Nadoooor/SnakeBoy/Images/3d Back PCB.png

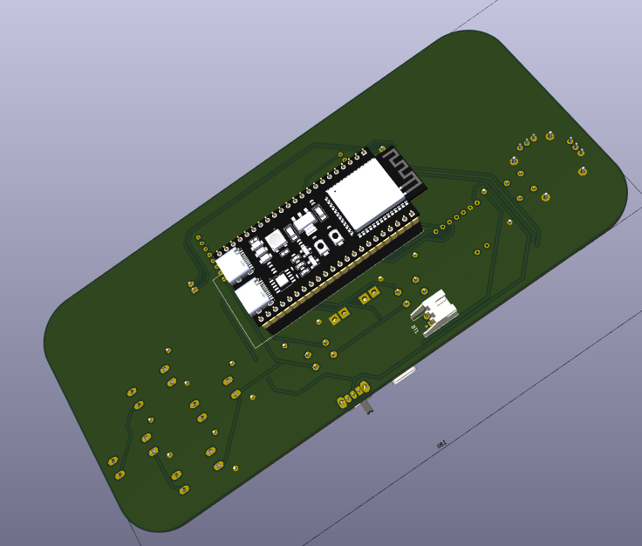
Images/3d Back PCB.png
