Nadoooor/SnakeBoy/Images/3D renders/33333.png

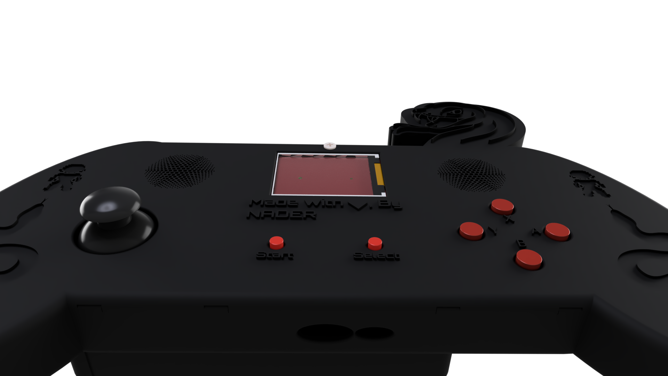
Images/3D renders/33333.png
