Nadoooor/SnakeBoy/Images/3D renders/i hope'.png

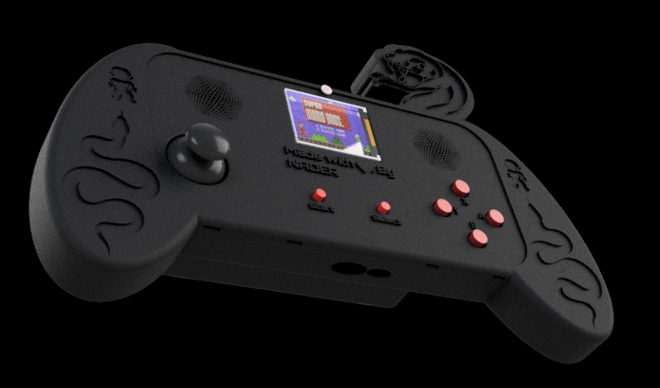
Images/3D renders/i hope'.png
