Nadoooor/SnakeBoy/Images/3D renders/Purple.PNG

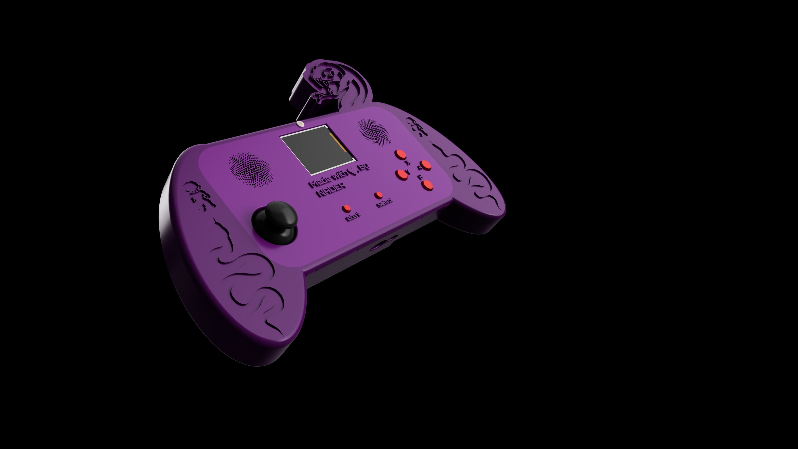
Images/3D renders/Purple.PNG
