Nadoooor/SnakeBoy/Images/3D renders/Thisone.png

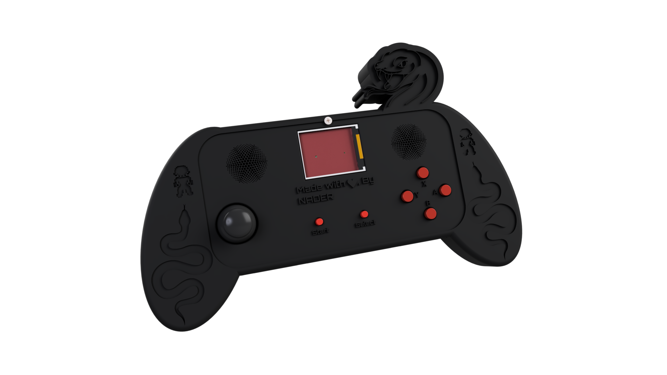
Images/3D renders/Thisone.png
