Nadoooor/SnakeBoy/Images/3D renders/Top transparent.png

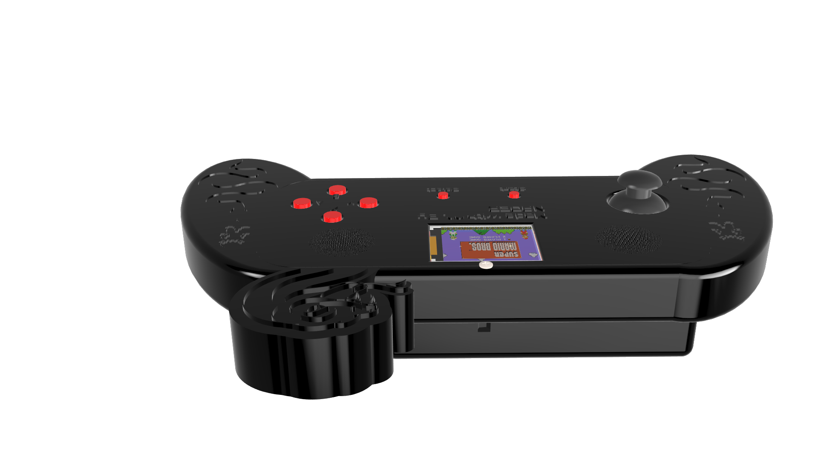
Images/3D renders/Top transparent.png
