Nadoooor/SnakeBoy/Images/3D renders/V2/Side.png

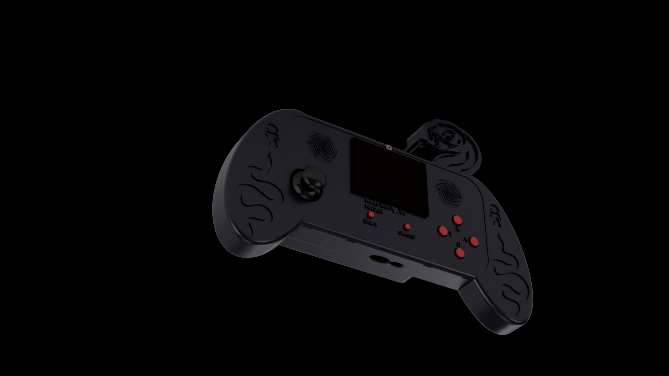
Images/3D renders/V2/Side.png
